MattRSON/RATLER/Board_RATLER/LogicBoard/LogicBoard.kicad_sch

## KiCad design Board_RATLER/LogicBoard/LogicBoard.kicad_sch (2026-02-09)

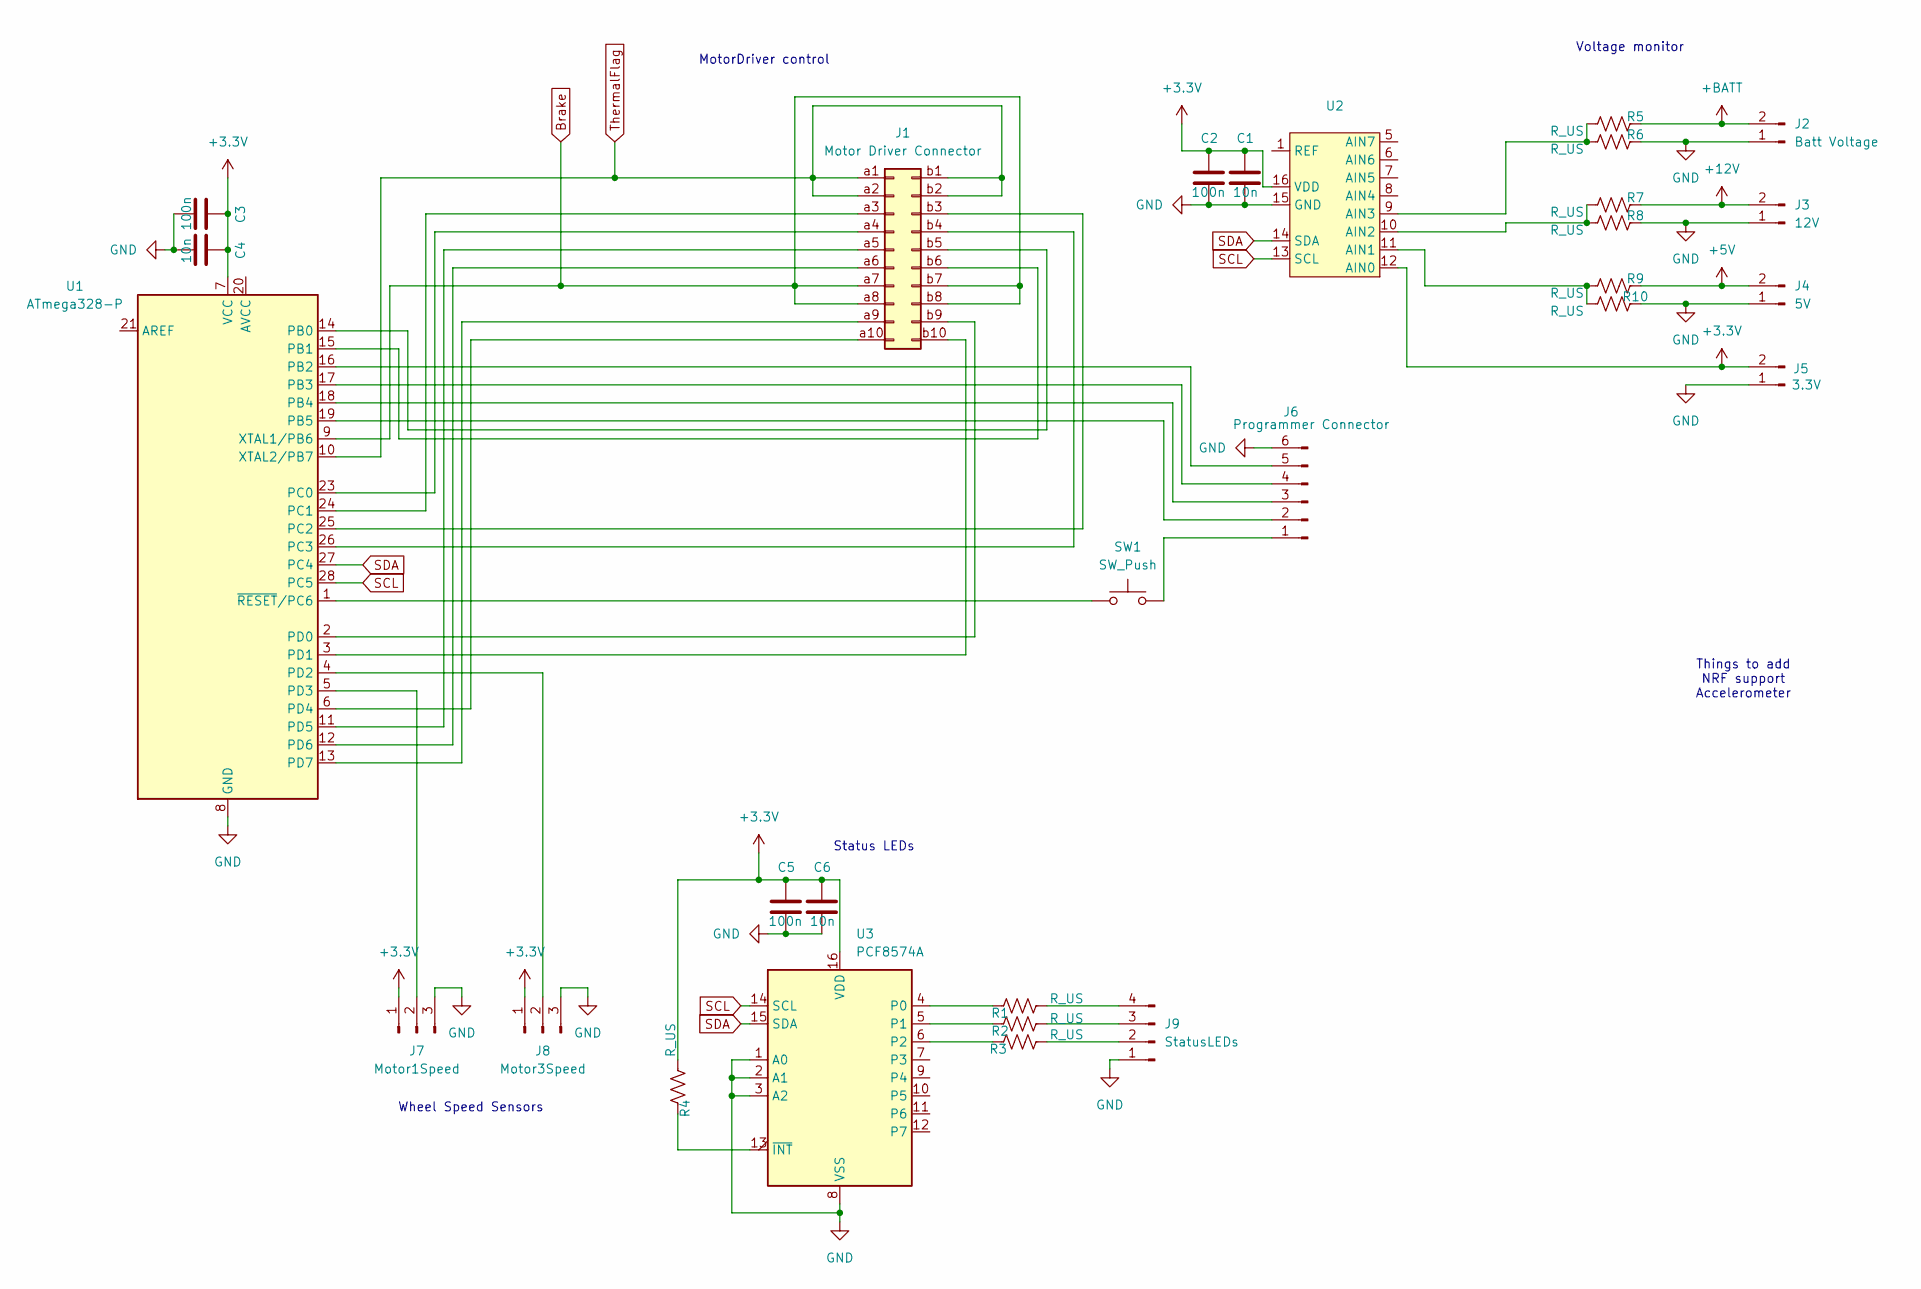
[picture p5: schematic LogicBoard.kicad_sch]

Parts:
C1, C4, C6: 10n
C2, C3, C5: 100n
J1: Motor Driver Connector
J2: Batt Voltage
J3: 12V
J4: 5V
J5: 3.3V
J6: Programmer Connector
J7: Motor1Speed
J8: Motor3Speed
J9: StatusLEDs
R1, R2, R3, R4, R5, R6, R7, R8, R9, R10: R_US
SW1: SW_Push
U1: ATmega328-P; DIP-28_W7.62mm
U2: (no value)
U3: PCF8574A

Connections:
+3.3V: C1.1, C2.1, C3.1, C4.1, C5.1, C6.1, J5.2, J7.1, J8.1, R4.2, U1.7 (VCC), U2.12 (AIN0), U2.16 (VDD), U3.16 (VDD)
+5V: J4.2, R9.1
+12V: J3.2, R7.1
+BATT: J2.2, R5.1
Brake: J1.a7, J1.a8, J1.b7, J1.b8, U1.9 (XTAL1/PB6)
GND: C1.2, C2.2, C3.2, C4.2, C5.2, C6.2, J2.1, J3.1, J4.1, J5.1, J6.6, J7.3, J8.3, J9.1, R6.1, R8.1, R10.1, U1.8 (GND), U1.22 (GND), U2.15 (GND), U3.1 (A0), U3.2 (A1), U3.3 (A2), U3.8 (VSS)
unnamed: J1.a3, U1.24 (PC1)
unnamed: J1.a4, U1.23 (PC0)
unnamed: J1.a5, U1.11 (PD5)
unnamed: J1.a6, U1.12 (PD6)
unnamed: J1.a9, U1.13 (PD7)
unnamed: J1.a10, U1.6 (PD4)
unnamed: J1.b3, U1.25 (PC2)
unnamed: J1.b4, U1.26 (PC3)
unnamed: J1.b5, U1.14 (PB0)
unnamed: J1.b6, U1.15 (PB1)
unnamed: J1.b9, U1.2 (PD0)
unnamed: J1.b10, U1.3 (PD1)
unnamed: J6.1, SW1.2
unnamed: J6.2, U1.19 (PB5)
unnamed: J6.3, U1.18 (PB4)
unnamed: J6.4, U1.17 (PB3)
unnamed: J6.5, U1.16 (PB2)
unnamed: J7.2, U1.5 (PD3)
unnamed: J8.2, U1.4 (PD2)
unnamed: J9.2, R3.2
unnamed: J9.3, R2.2
unnamed: J9.4, R1.2
unnamed: R1.1, U3.4 (P0)
unnamed: R2.1, U3.5 (P1)
unnamed: R3.1, U3.6 (P2)
unnamed: R4.1, U3.13 (~INT)
unnamed: R5.2, R6.2, U2.9 (AIN3)
unnamed: R7.2, R8.2, U2.10 (AIN2)
unnamed: R9.2, R10.2, U2.11 (AIN1)
unnamed: SW1.1, U1.1 (~RESET/PC6)
SCL: U1.28 (PC5), U2.13 (SCL), U3.14 (SCL)
SDA: U1.27 (PC4), U2.14 (SDA), U3.15 (SDA)
ThermalFlag: J1.a1, J1.a2, J1.b1, J1.b2, U1.10 (XTAL2/PB7)

Notes on the sheet:
Voltage monitor
Things to add NRF support Accelerometer
MotorDriver control
Status LEDs
Wheel Speed Sensors
